amcorbit/UCB_v2.0/Photos/Image (3).jpg

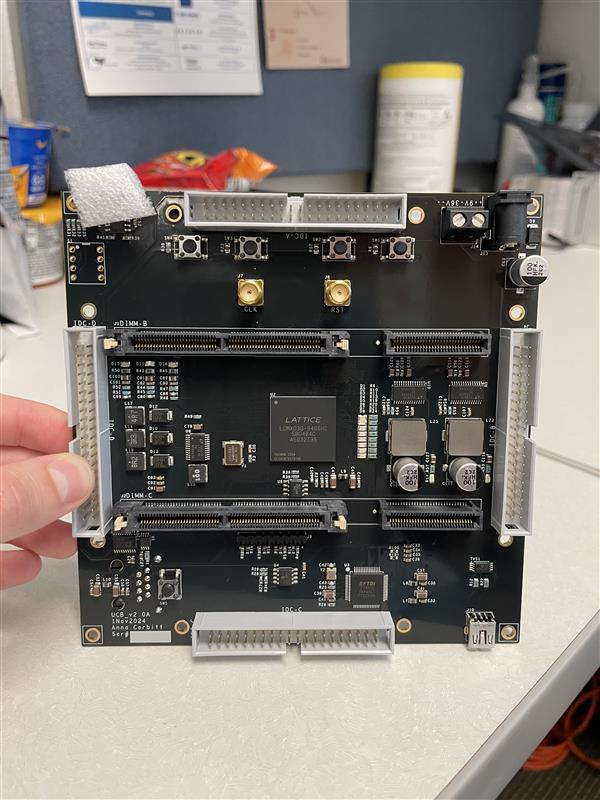
Photos/Image (3).jpg
