amcorbit/UCB_v2.0/Old_UCB_v1.4a_Archive/Schematics/Schematic-UCB_PE-EVAL_V1.5.pdf

# Isolated Voltage Sensing

## Scale : (R39, R45, R51, R57, R63, and R69)

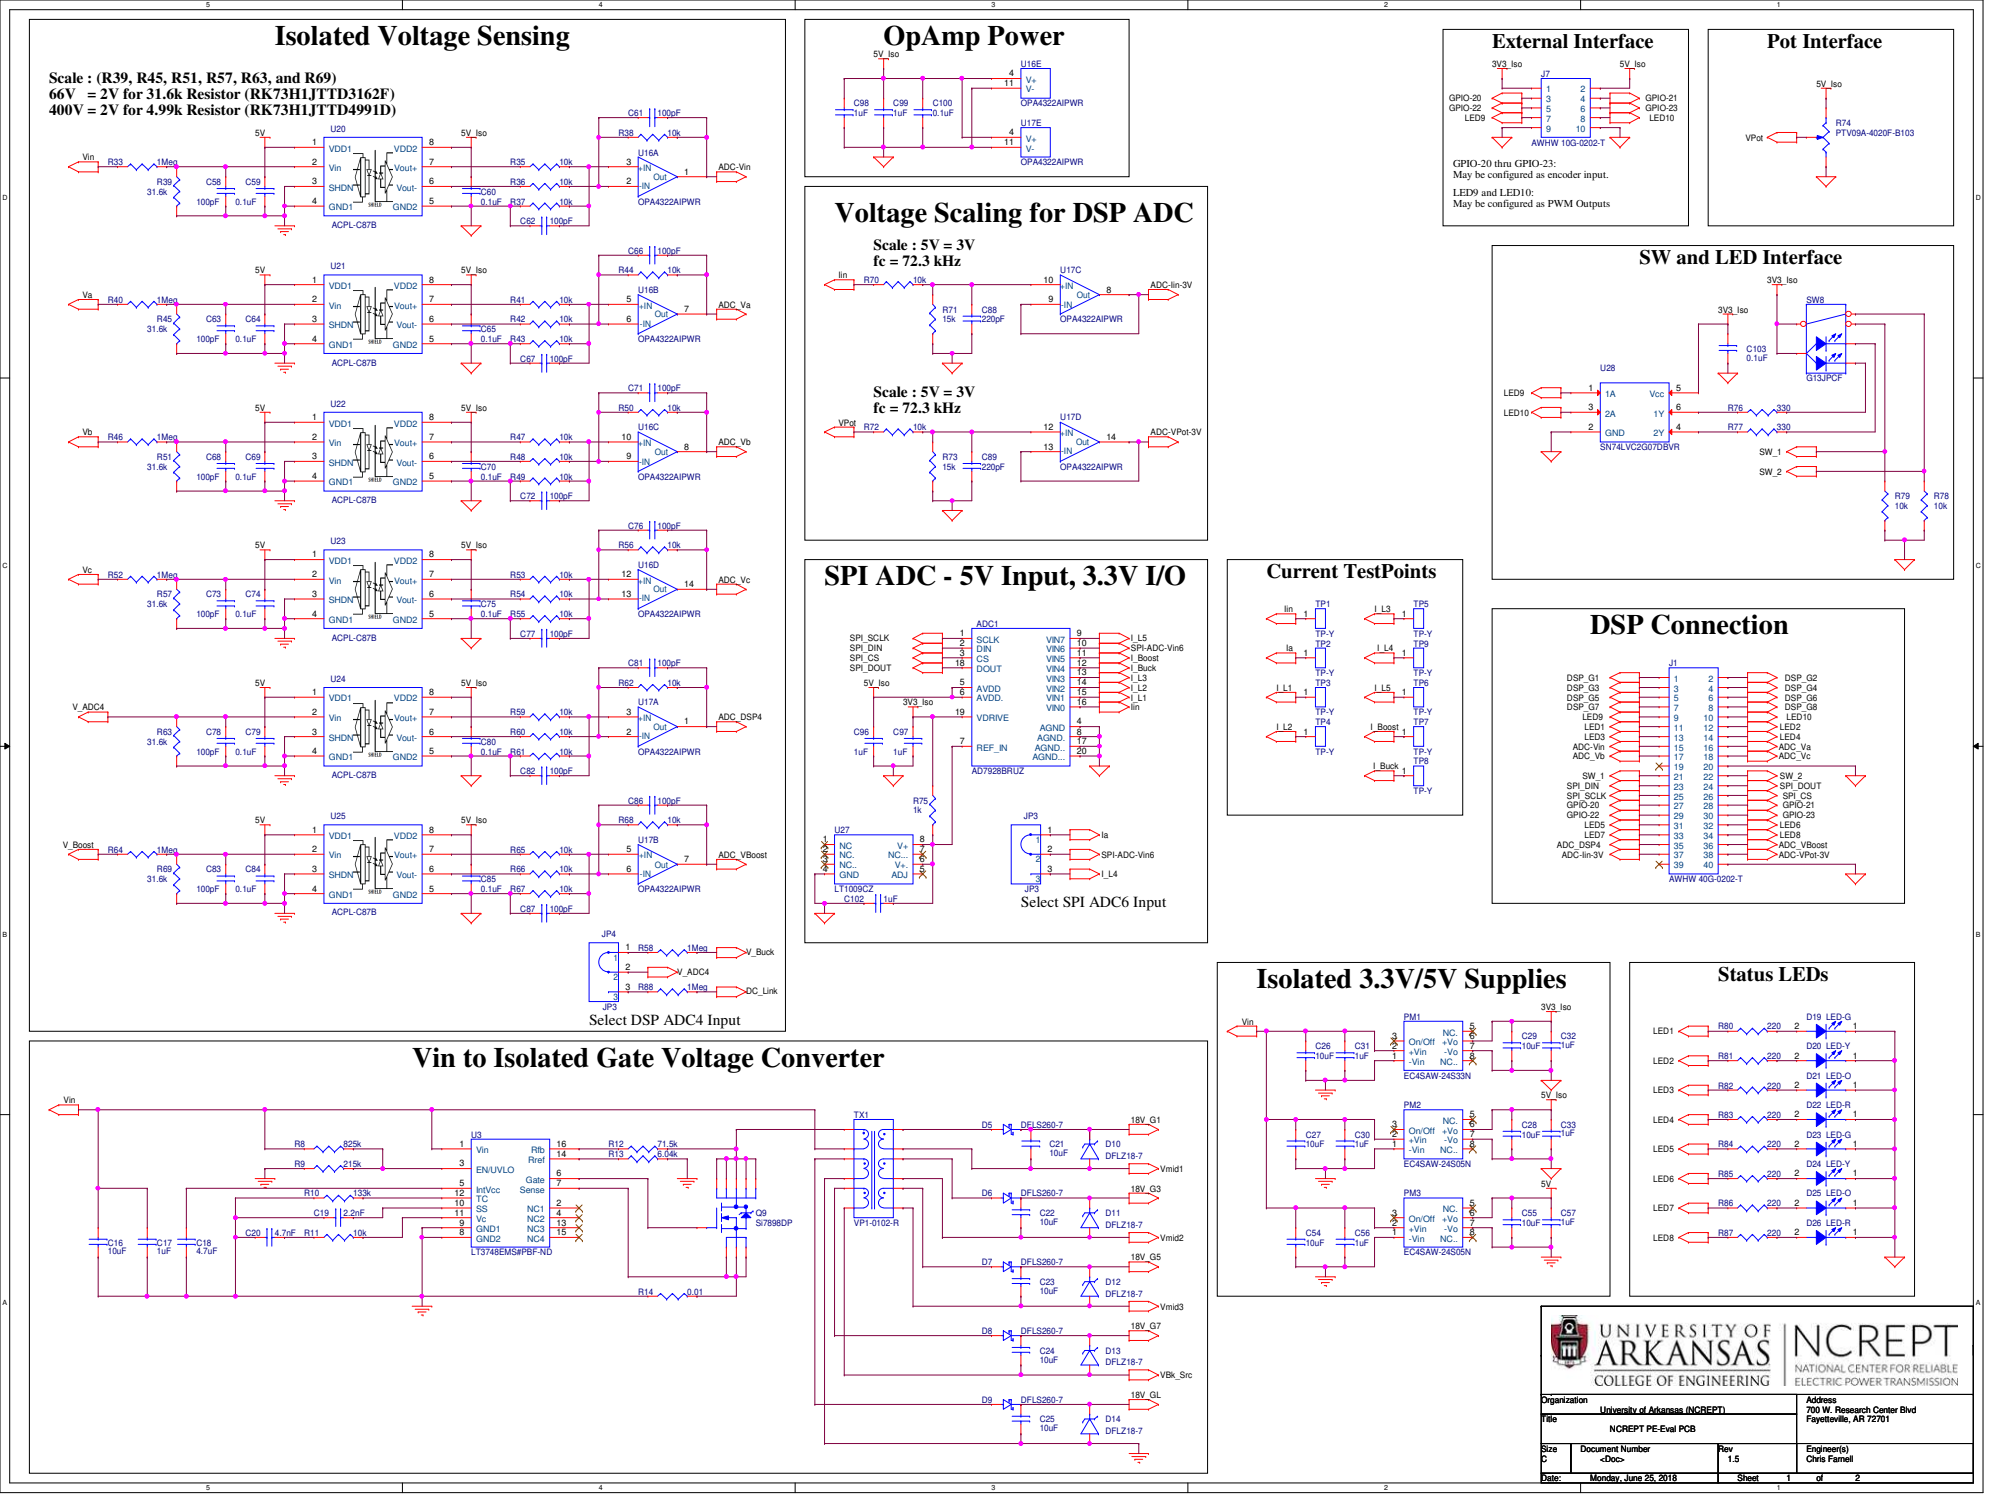
[picture p31: page 1]

GPIO-20 thru GPIO-23:
May be configured as encoder input.
LED9 and LED10:
May be configured as PWM Outputs

Voltage Scaling for DSP ADC

SW and LED Interface

Vin to Isolated Gate Voltage Converter

University of Arkansas (NCREPT)

NCREPT PE-Eval PCB

# Buck Converter (50V Max)

# DC Power Entry (9V-36V)

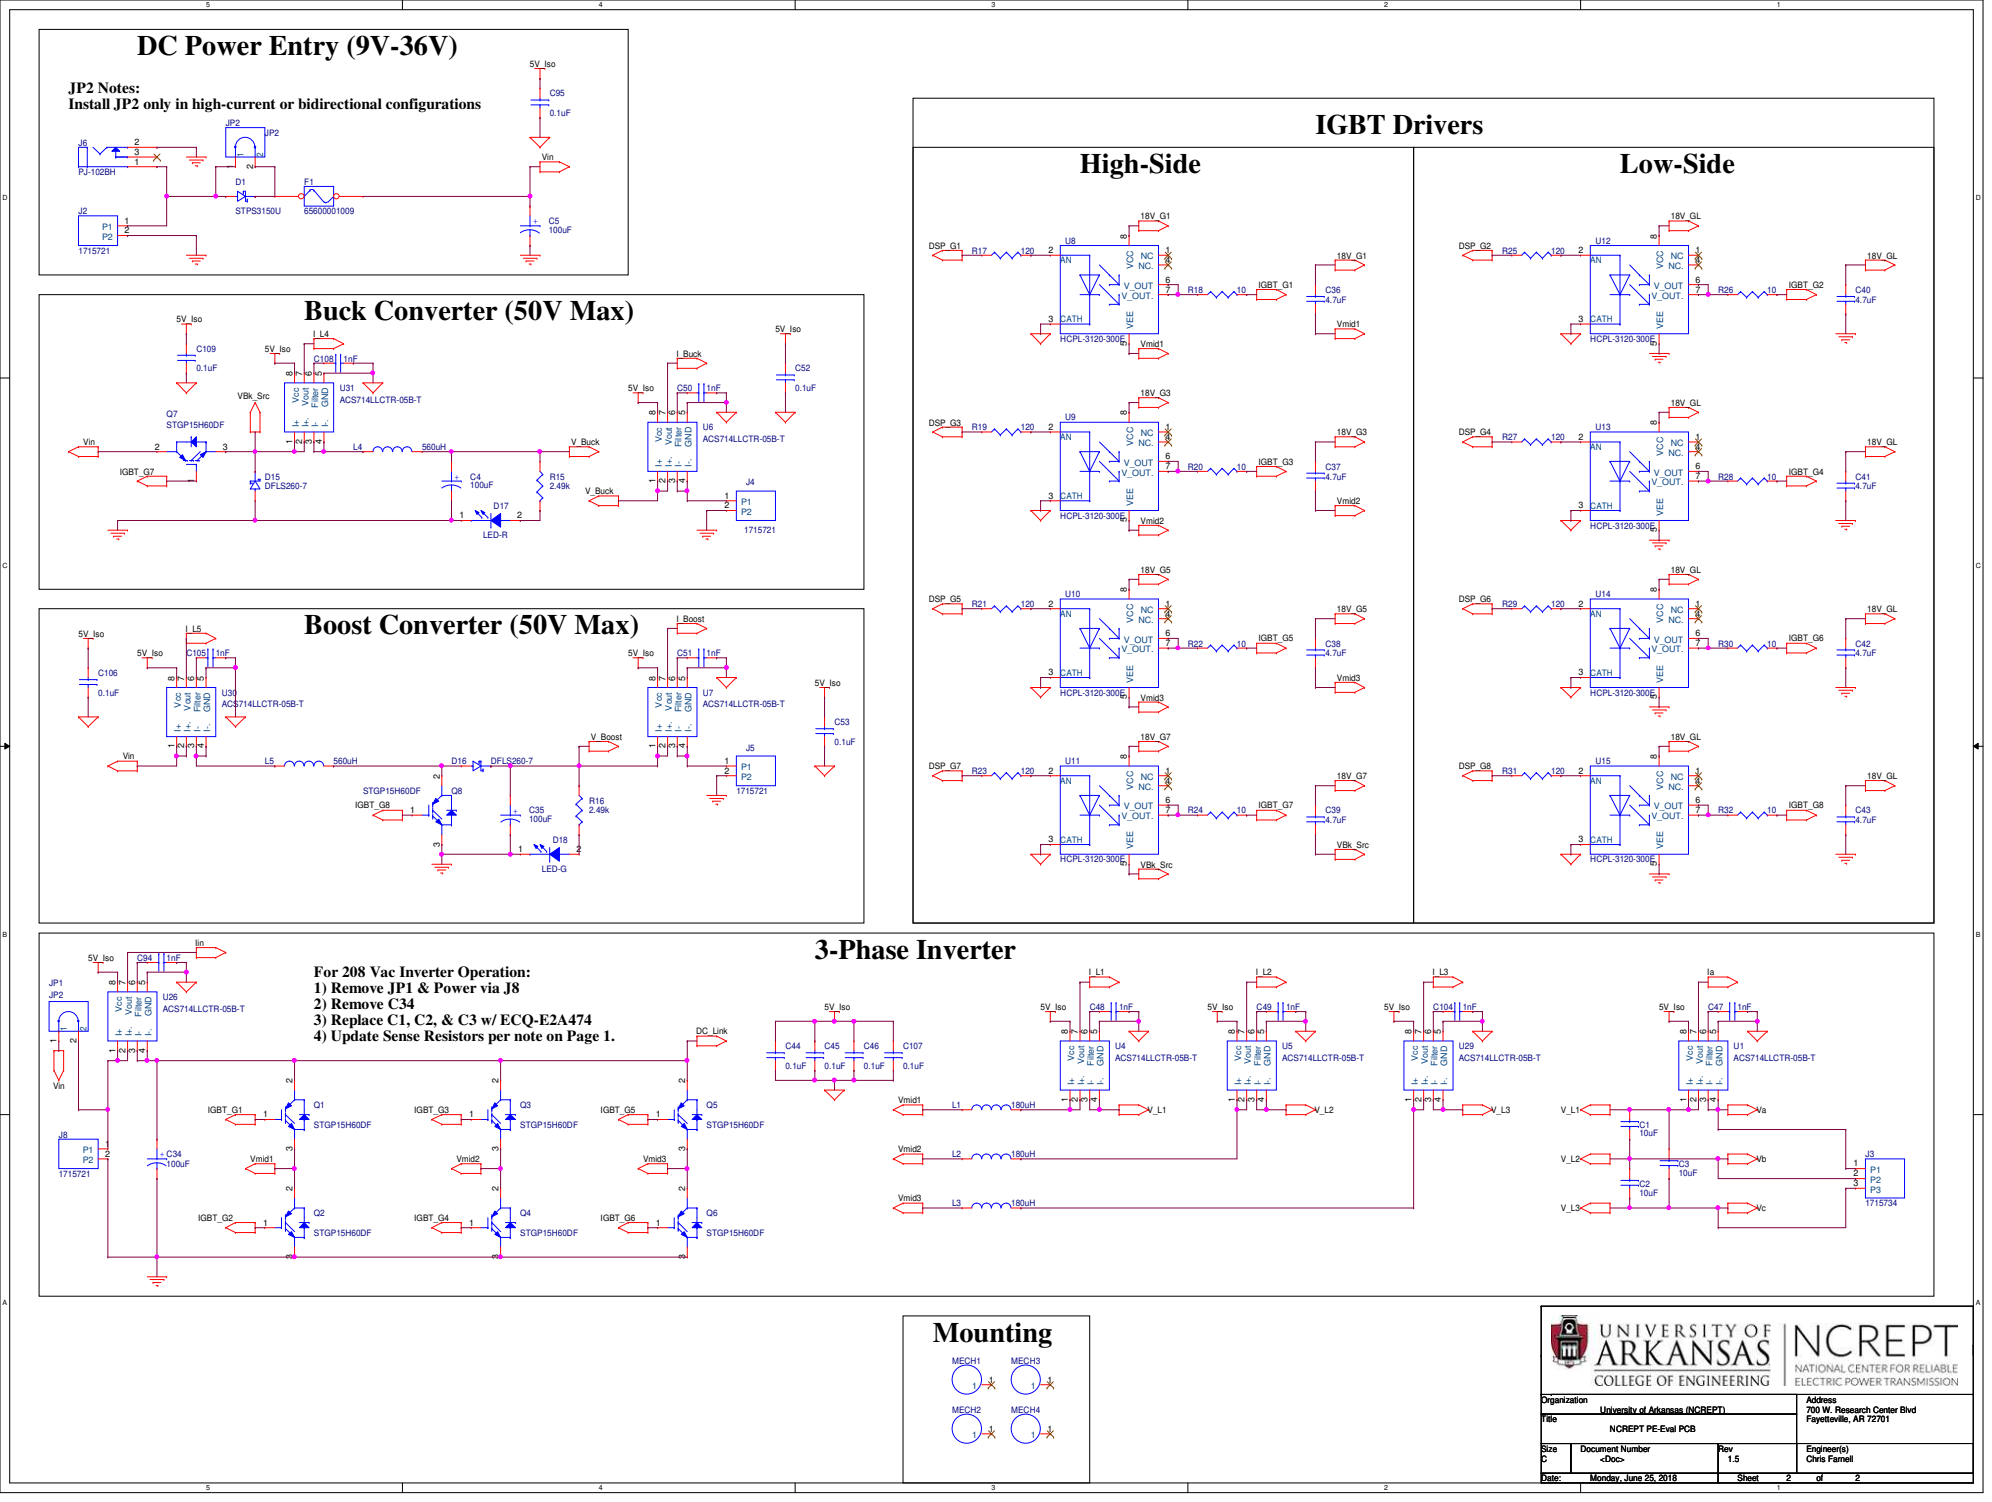
[picture p32: page 2]

JP2 Notes:
Install JP2 only in high-current or bidirectional configurations

For 208 Vac Inverter Operation:
1) Remove JP1 & Power via J8
2) Remove C34
3) Replace C1, C2, & C3 w/ ECQ-E2A474

4) Update Sense Resistors per note on Page 1.

University of Arkansas (NCREPT)

NCREPT PE-Eval PCB
