amcorbit/UCB_v2.0/Photos/IMG_9684 (1).jpeg

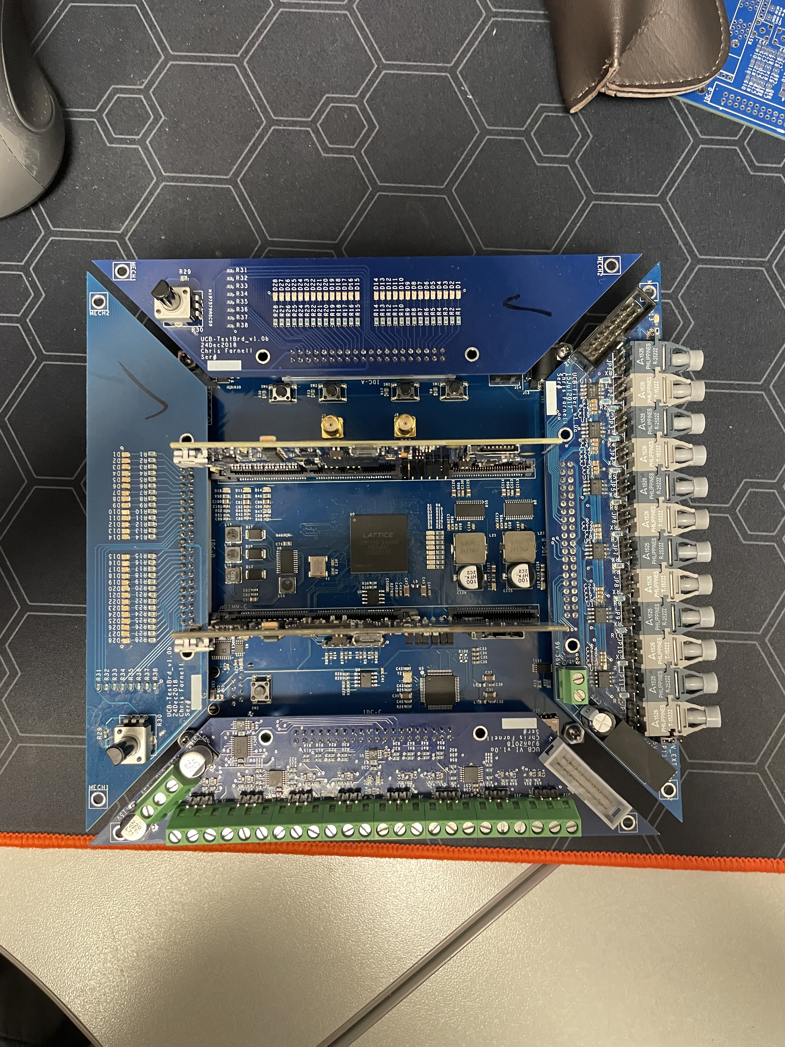
Photos/IMG_9684 (1).jpeg
