amcorbit/UCB_v2.0/Photos/IMG_9694 (1).jpeg

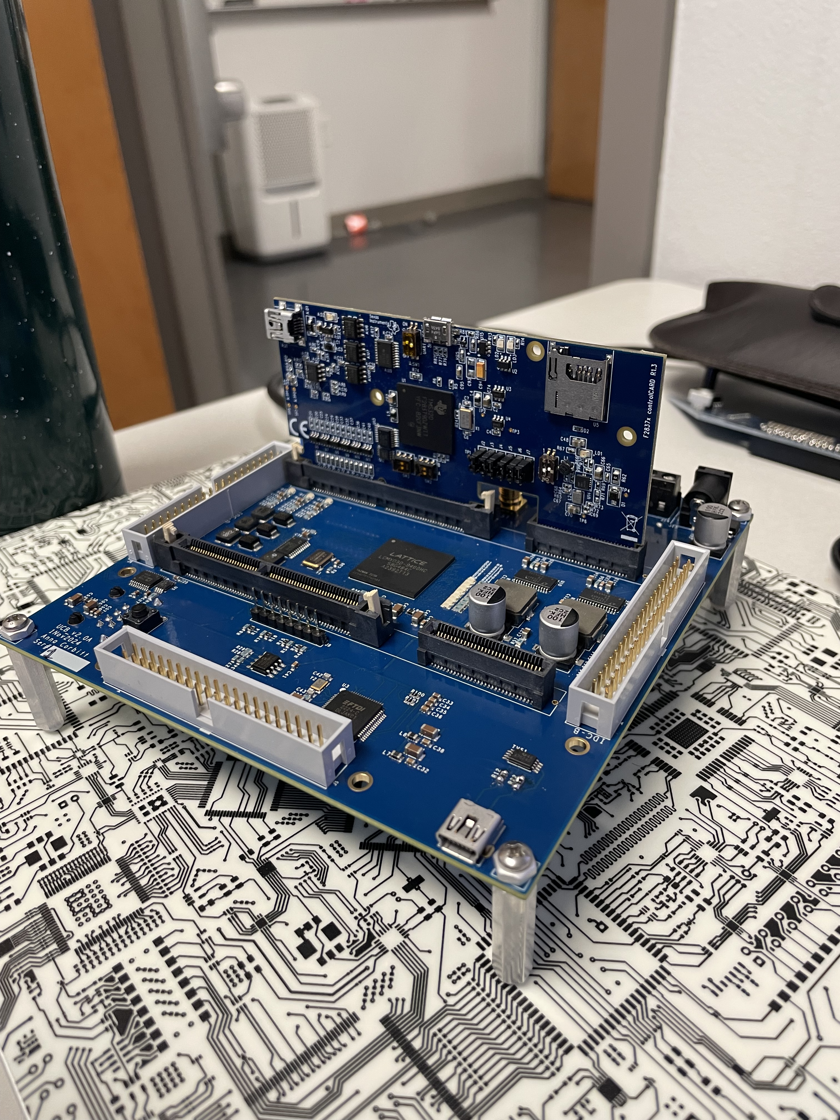
Photos/IMG_9694 (1).jpeg
